sergei-nntu/orm/mechanics/ORM-1. PT2/14_1_6.stl

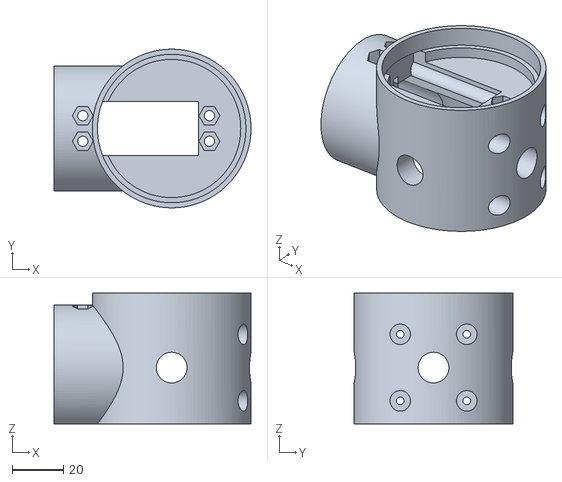
[picture p15: CAD file, 2024-07-11]
mechanics/ORM-1. PT2/14_1_6.stl
77.0 x 62.0 x 51.1
