sergei-nntu/orm/mechanics/9_13_2.stl

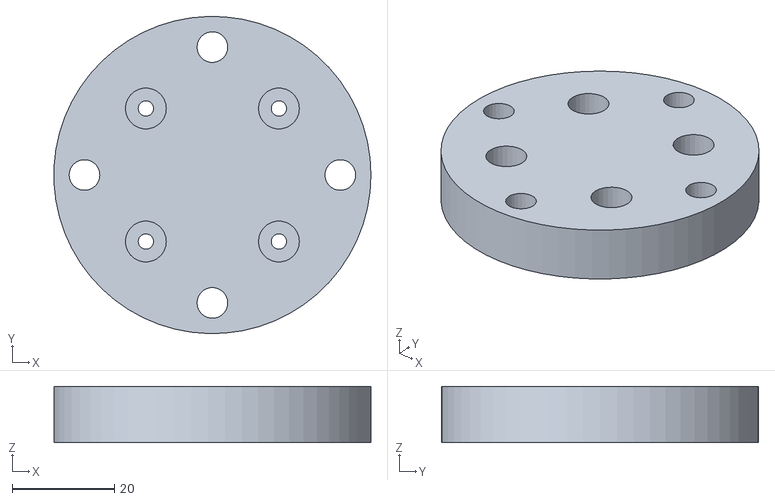
[picture p16: CAD file, 2023-09-25]
mechanics/9_13_2.stl
62.0 x 62.0 x 11.0
