sergei-nntu/orm/mechanics/ORM-1. PT2/15_1_5.stl

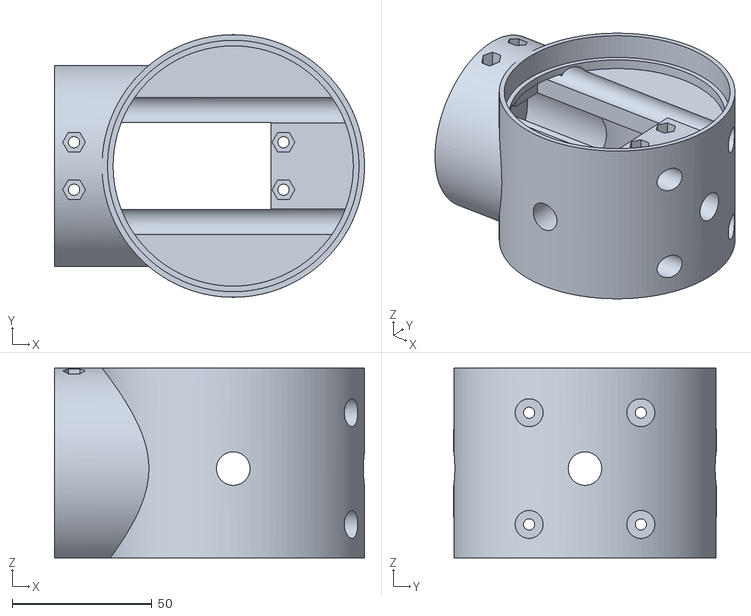
[picture p17: CAD file, 2024-07-11]
mechanics/ORM-1. PT2/15_1_5.stl
111.0 x 94.0 x 68.0
