sergei-nntu/orm/mechanics/ORM-1. PT2/15_3_2.stl

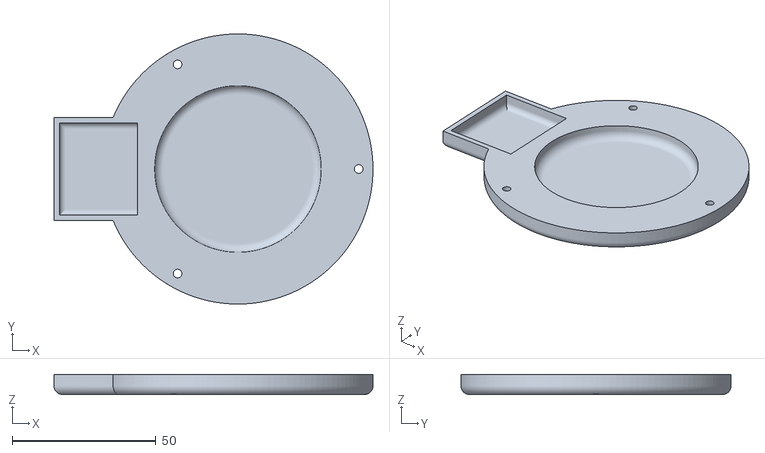
[picture p18: CAD file, 2024-07-11]
mechanics/ORM-1. PT2/15_3_2.stl
111.0 x 94.0 x 7.00
