sergei-nntu/orm/mechanics/9_8_1.stl

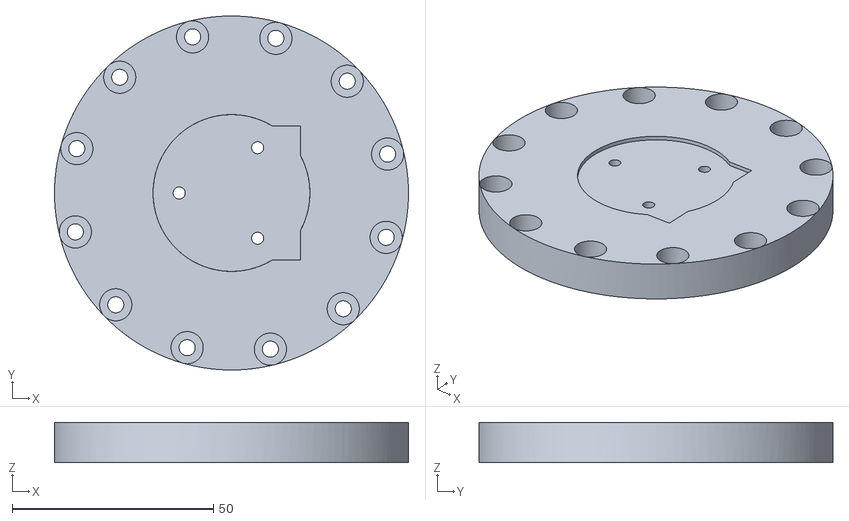
[picture p19: CAD file, 2023-09-14]
mechanics/9_8_1.stl
88.0 x 88.0 x 10.0
