sergei-nntu/orm/mechanics/9_14_1.stl

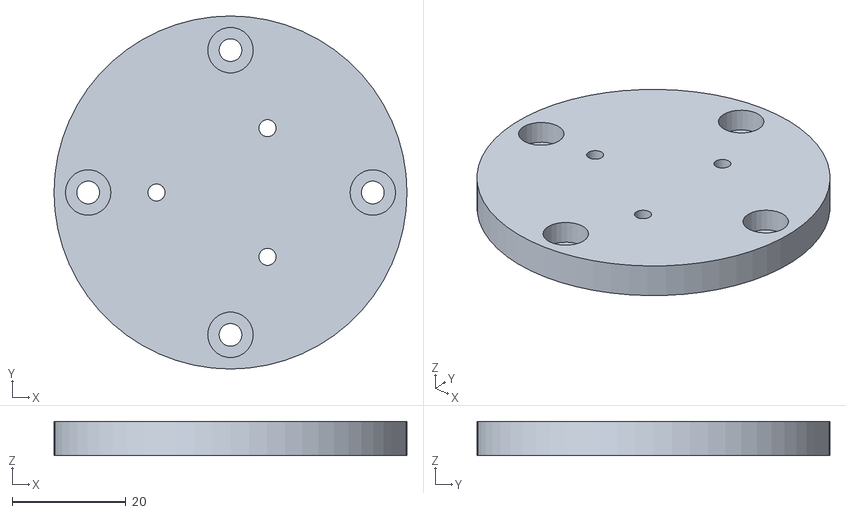
[picture p20: CAD file, 2023-09-14]
mechanics/9_14_1.stl
62.0 x 62.0 x 6.00
