sergei-nntu/orm/mechanics/ShoulderActuator.stl

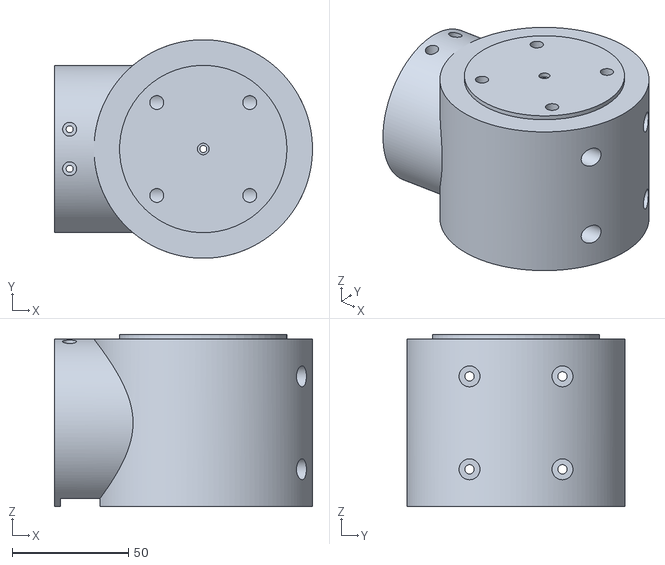
[picture p21: CAD file, 2023-09-14]
mechanics/ShoulderActuator.stl
111.0 x 94.0 x 74.0
