sergei-nntu/orm/mechanics/9_9_1.stl

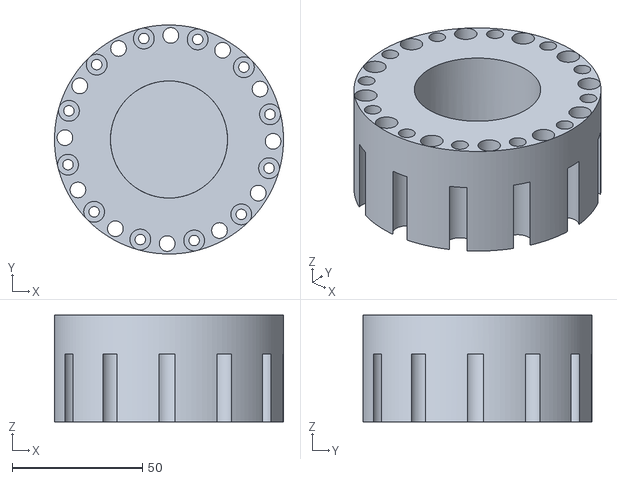
[picture p22: CAD file, 2023-09-14]
mechanics/9_9_1.stl
88.0 x 88.0 x 41.0
