sergei-nntu/orm/mechanics/9_1_2.stl

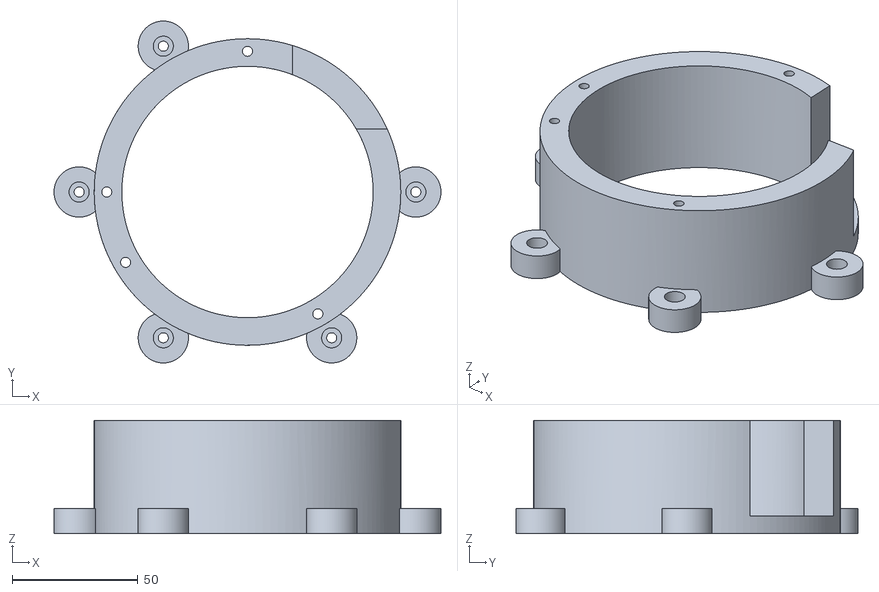
[picture p23: CAD file, 2023-09-14]
mechanics/9_1_2.stl
154.0 x 136.0 x 45.0
