sergei-nntu/orm/mechanics/9_10_1.stl

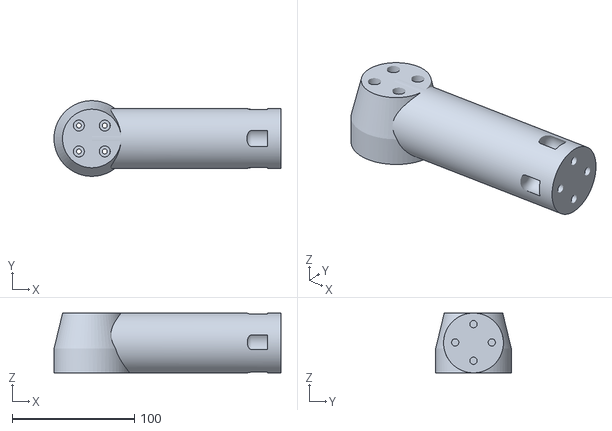
[picture p24: CAD file, 2023-09-14]
mechanics/9_10_1.stl
186.0 x 62.0 x 49.1
