sergei-nntu/orm/mechanics/9_5_1.stl

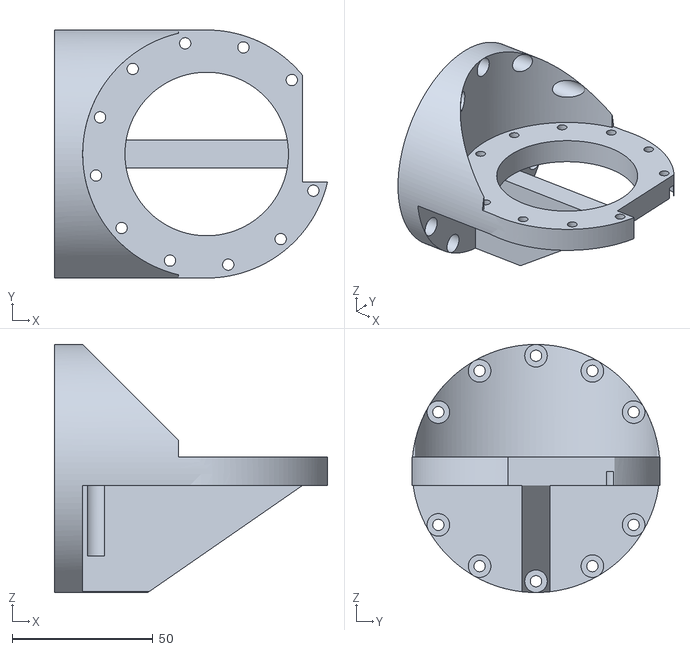
[picture p25: CAD file, 2023-05-16]
mechanics/9_5_1.stl
96.8 x 88.0 x 88.0
