sergei-nntu/orm/mechanics/9_6_1.stl

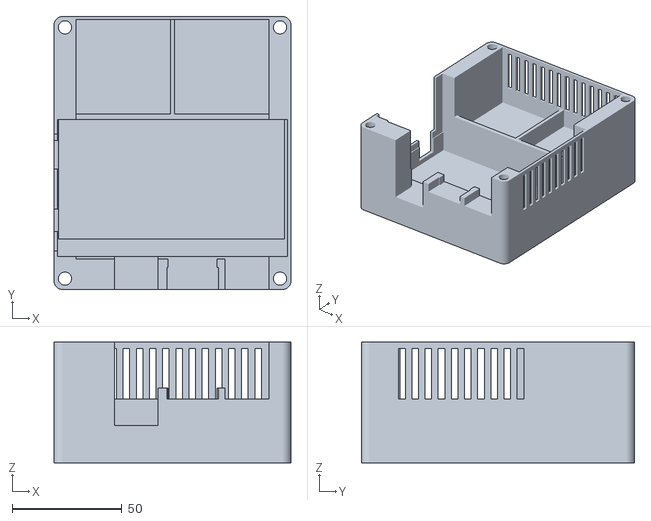
[picture p26: CAD file, 2023-05-16]
mechanics/9_6_1.stl
108.0 x 124.5 x 55.0
