sergei-nntu/orm/mechanics/9_7_1.stl

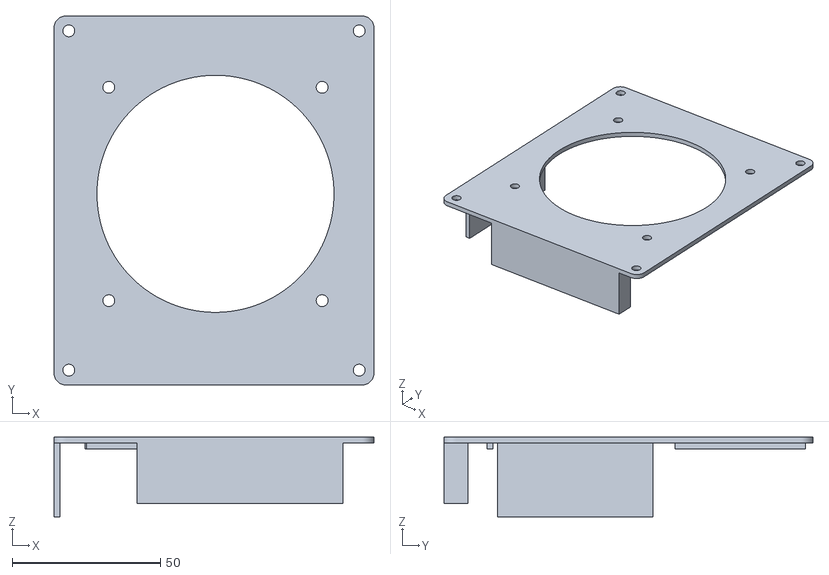
[picture p27: CAD file, 2023-05-16]
mechanics/9_7_1.stl
108.0 x 124.5 x 27.0
