sergei-nntu/orm/mechanics/9_4_1.stl

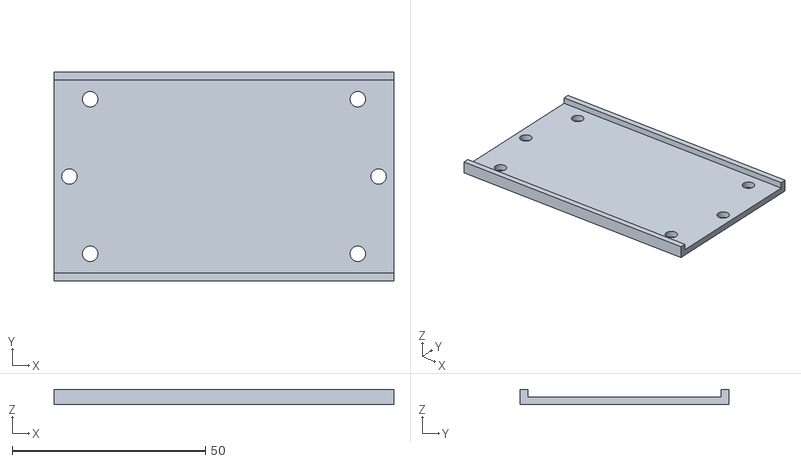
[picture p28: CAD file, 2023-05-16]
mechanics/9_4_1.stl
88.0 x 54.0 x 4.00
