sergei-nntu/orm/mechanics/ORM-1 Controller Block.FCStd

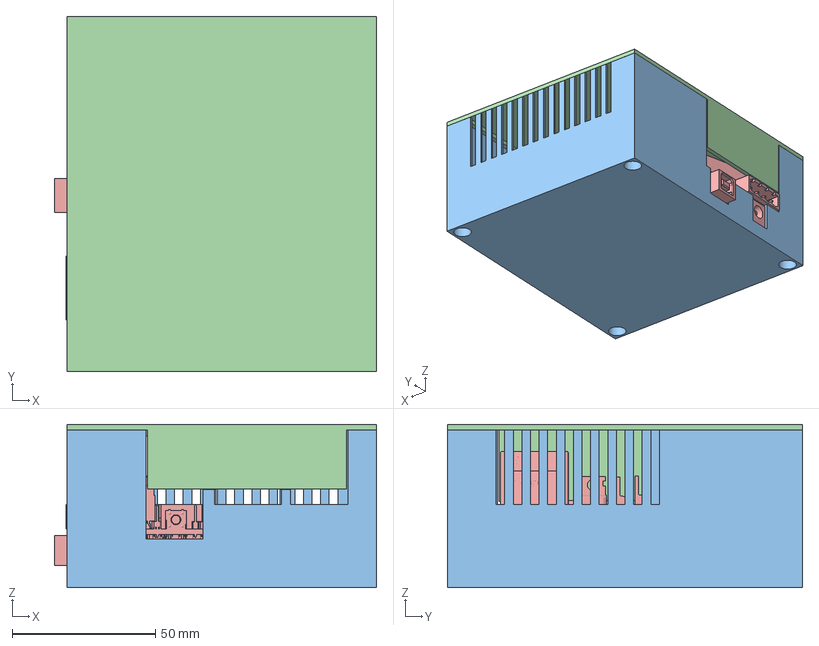
[picture p29: CAD file, 2023-05-16]
mechanics/ORM-1 Controller Block.FCStd
112.4 x 124.0 x 57.0 mm
A4988 Extension Board
A4988 Extension Board001
RAMPS1_4
